r4wabr/karabas_pro/docs/photos/karabas-pro-revB-top.png

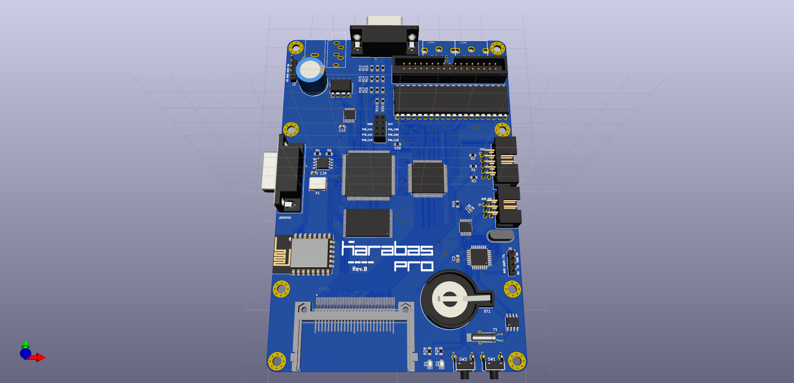
docs/photos/karabas-pro-revB-top.png
