r4wabr/karabas_pro/docs/photos/karabas-pro-revC-back.png

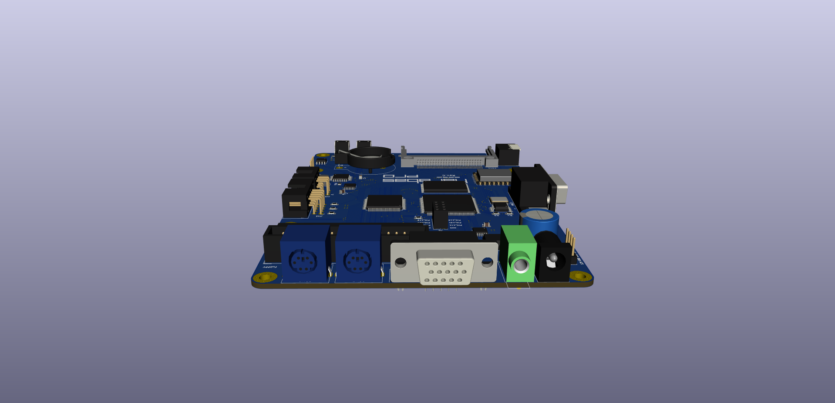
docs/photos/karabas-pro-revC-back.png
