r4wabr/karabas_pro/docs/photos/karabas-pro-revC-bot.png

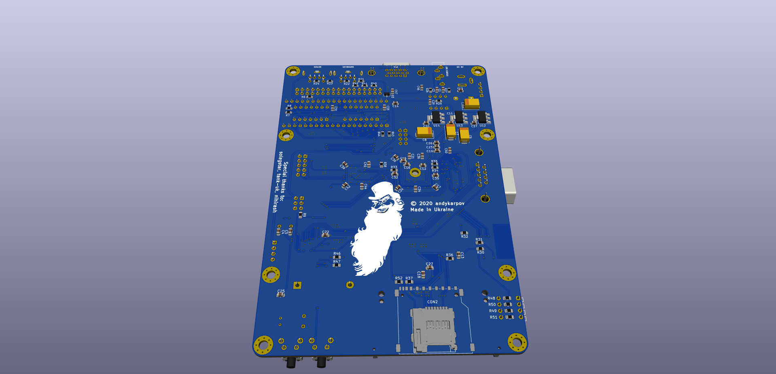
docs/photos/karabas-pro-revC-bot.png
