r4wabr/karabas_pro/docs/photos/karabas-pro-revC-top.png

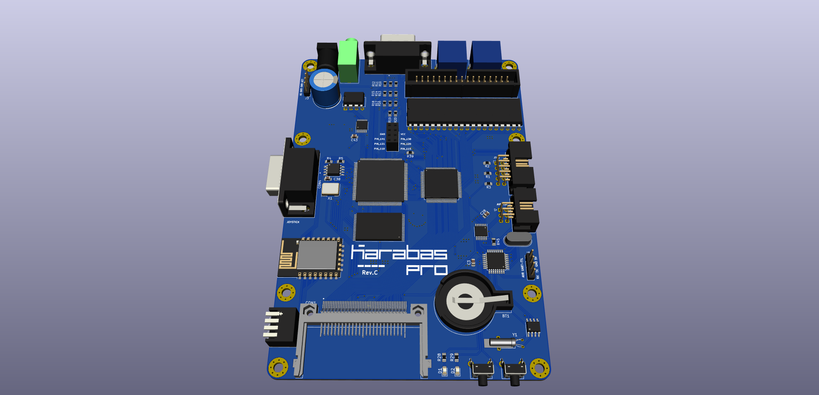
docs/photos/karabas-pro-revC-top.png
