r4wabr/karabas_pro/docs/photos/karabas-pro-revD-top.png

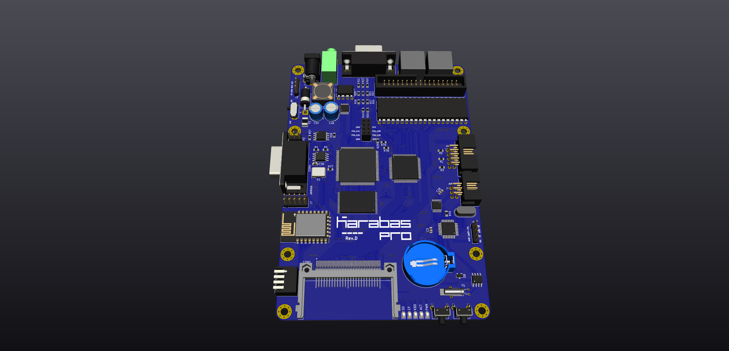
docs/photos/karabas-pro-revD-top.png
