r4wabr/karabas_pro/docs/photos/karabas-pro-revE-bot.png

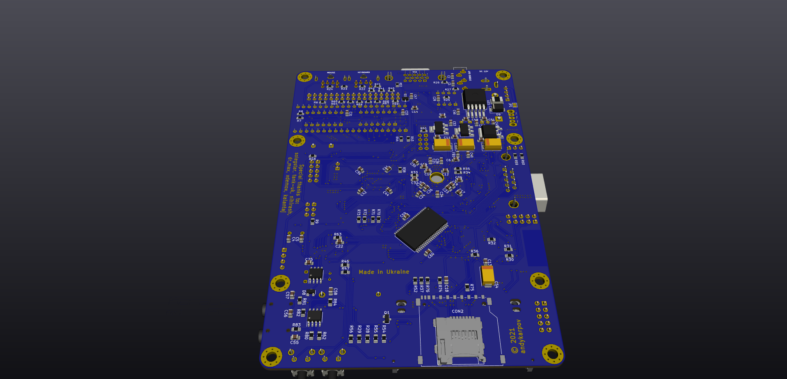
docs/photos/karabas-pro-revE-bot.png
