r4wabr/karabas_pro/docs/photos/karabas-pro-revE-top.png

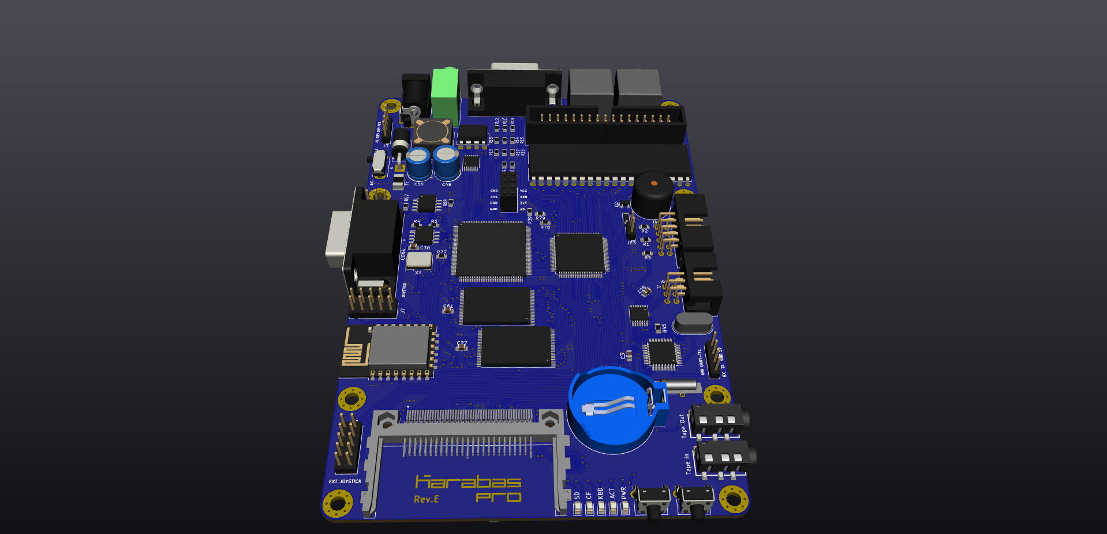
docs/photos/karabas-pro-revE-top.png
