r4wabr/karabas_pro/docs/photos/karabas-pro-revER-bottom.png

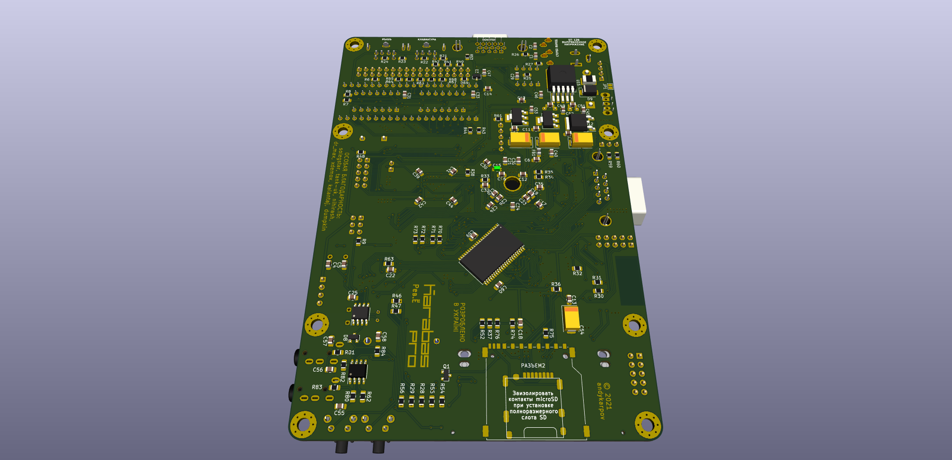
docs/photos/karabas-pro-revER-bottom.png
