r4wabr/karabas_pro/docs/karabas-pro-revD.pdf

# File: karabas-pro-revD.sch Sheet: / 100n C¹¹C7

# R10 2k R11 1k R12 510 R13 2k R14 1k R15 510 R16 2k R17 1k GND

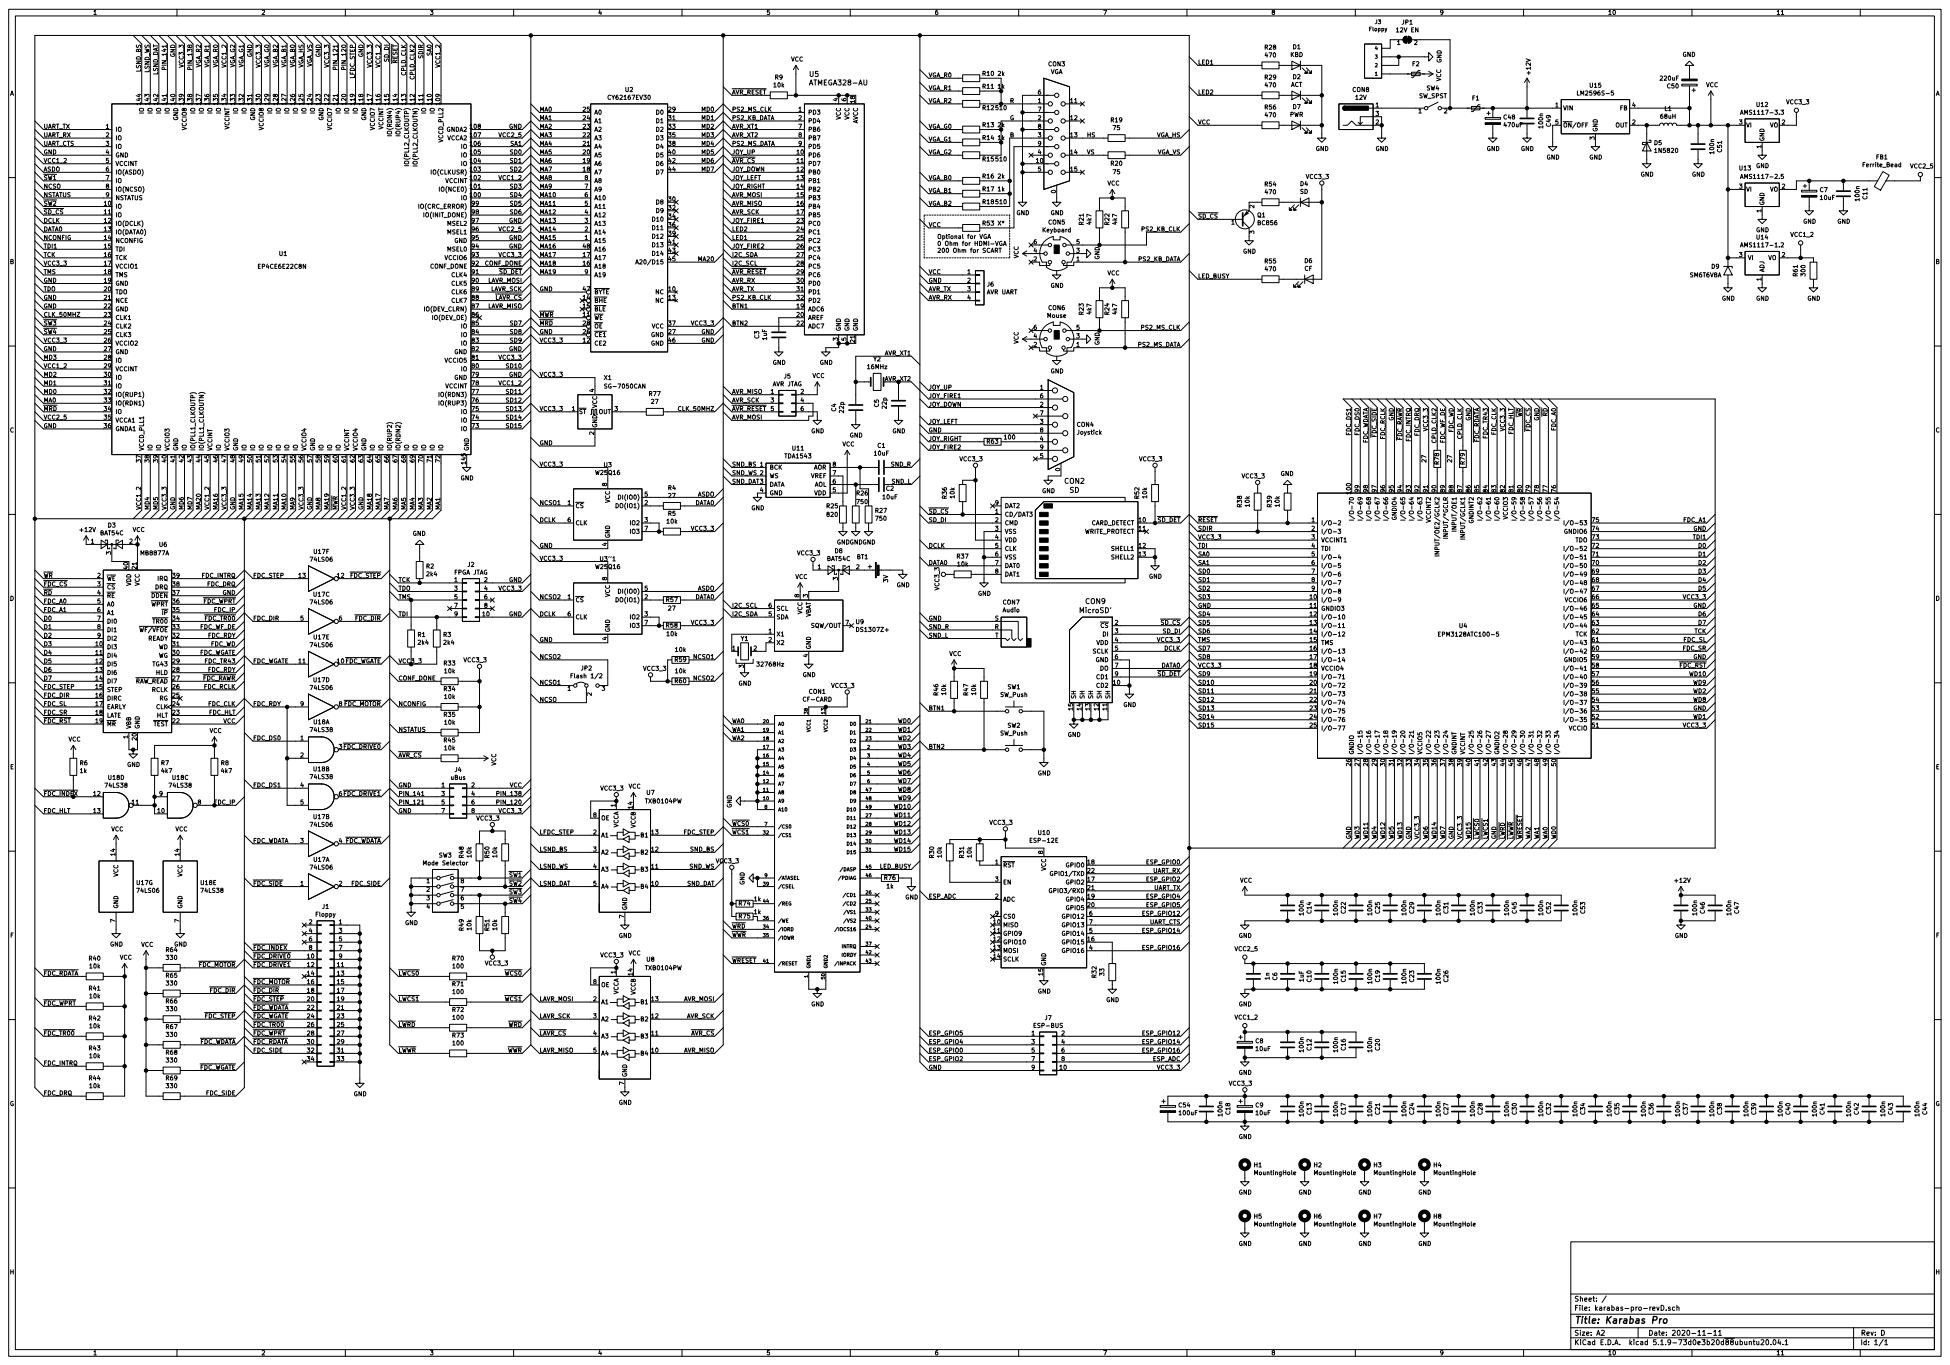
[picture p52: page 1]

6 PB6 7 PB7 8 PD5 9 PD6 10 AREF 20 PD0 30 PD7 11 GND 21 PD1 31 PB0 12 ADC7 22 PD2 32 PB1 13 PC0 23 PB2 14 PC1 24 PB3 15 PC2 25 PB4 16 PC3 26 PB5 17 PC4 27 AVCC 18 PC5 28 ADC6 19 PC6 29 U5ATMEGA328-AU

IO 2 TDO 20 NCE 21 GND 22 CLK1 23 CLK2 24 CLK3 25 VCCIO2 26 GND 27

Optional for VGA
0 Ohm for HDMI-VGA
200 Ohm for SCART

TDI 15 TCK 16 VCCIO1 17 TMS 18 GND 19
VCC1_2 TDO
VCC3_3 CLK_50MHZ GND

IP 35 WPRT 36 DDEN 37 DRQ 38

4 SDA 5 SCL 6 SQW/OUT 7 VCC

Id: 1/1 Title: Karabas Pro

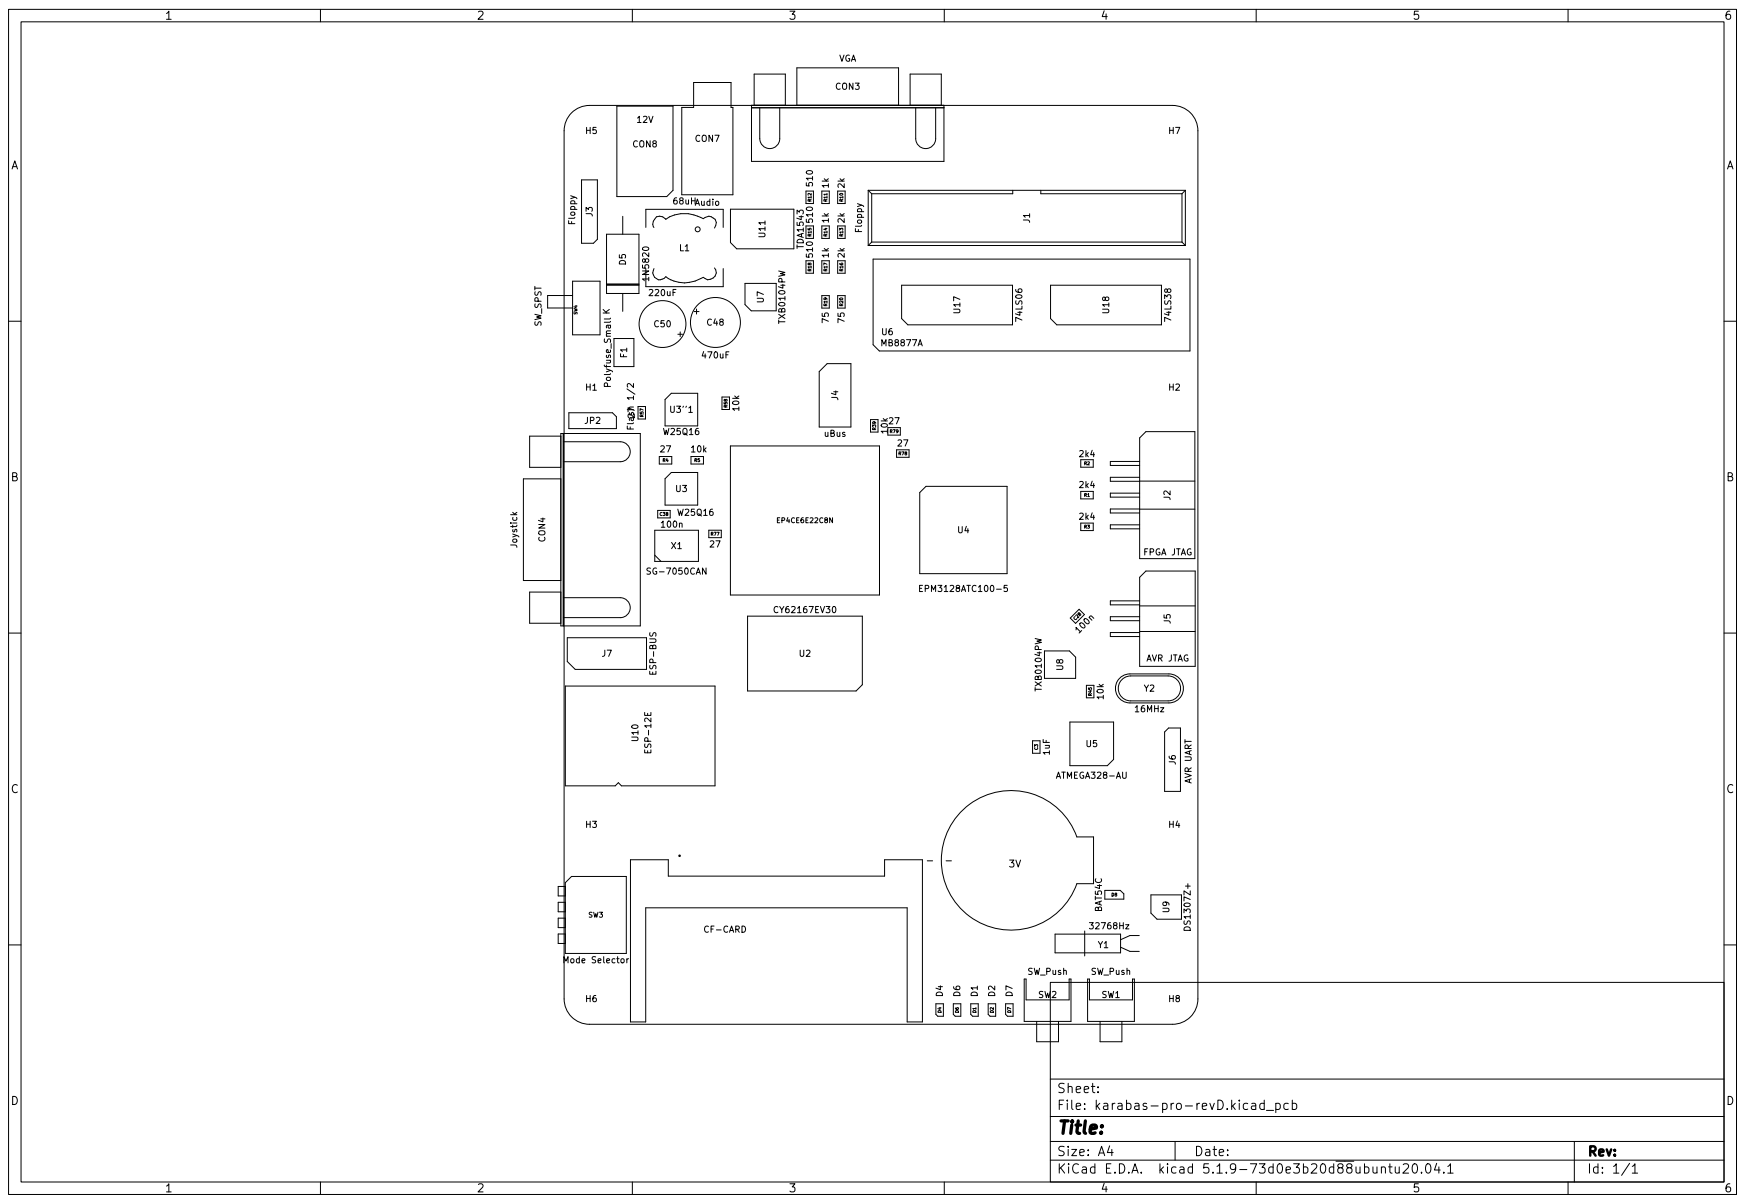
[picture p53: page 2]

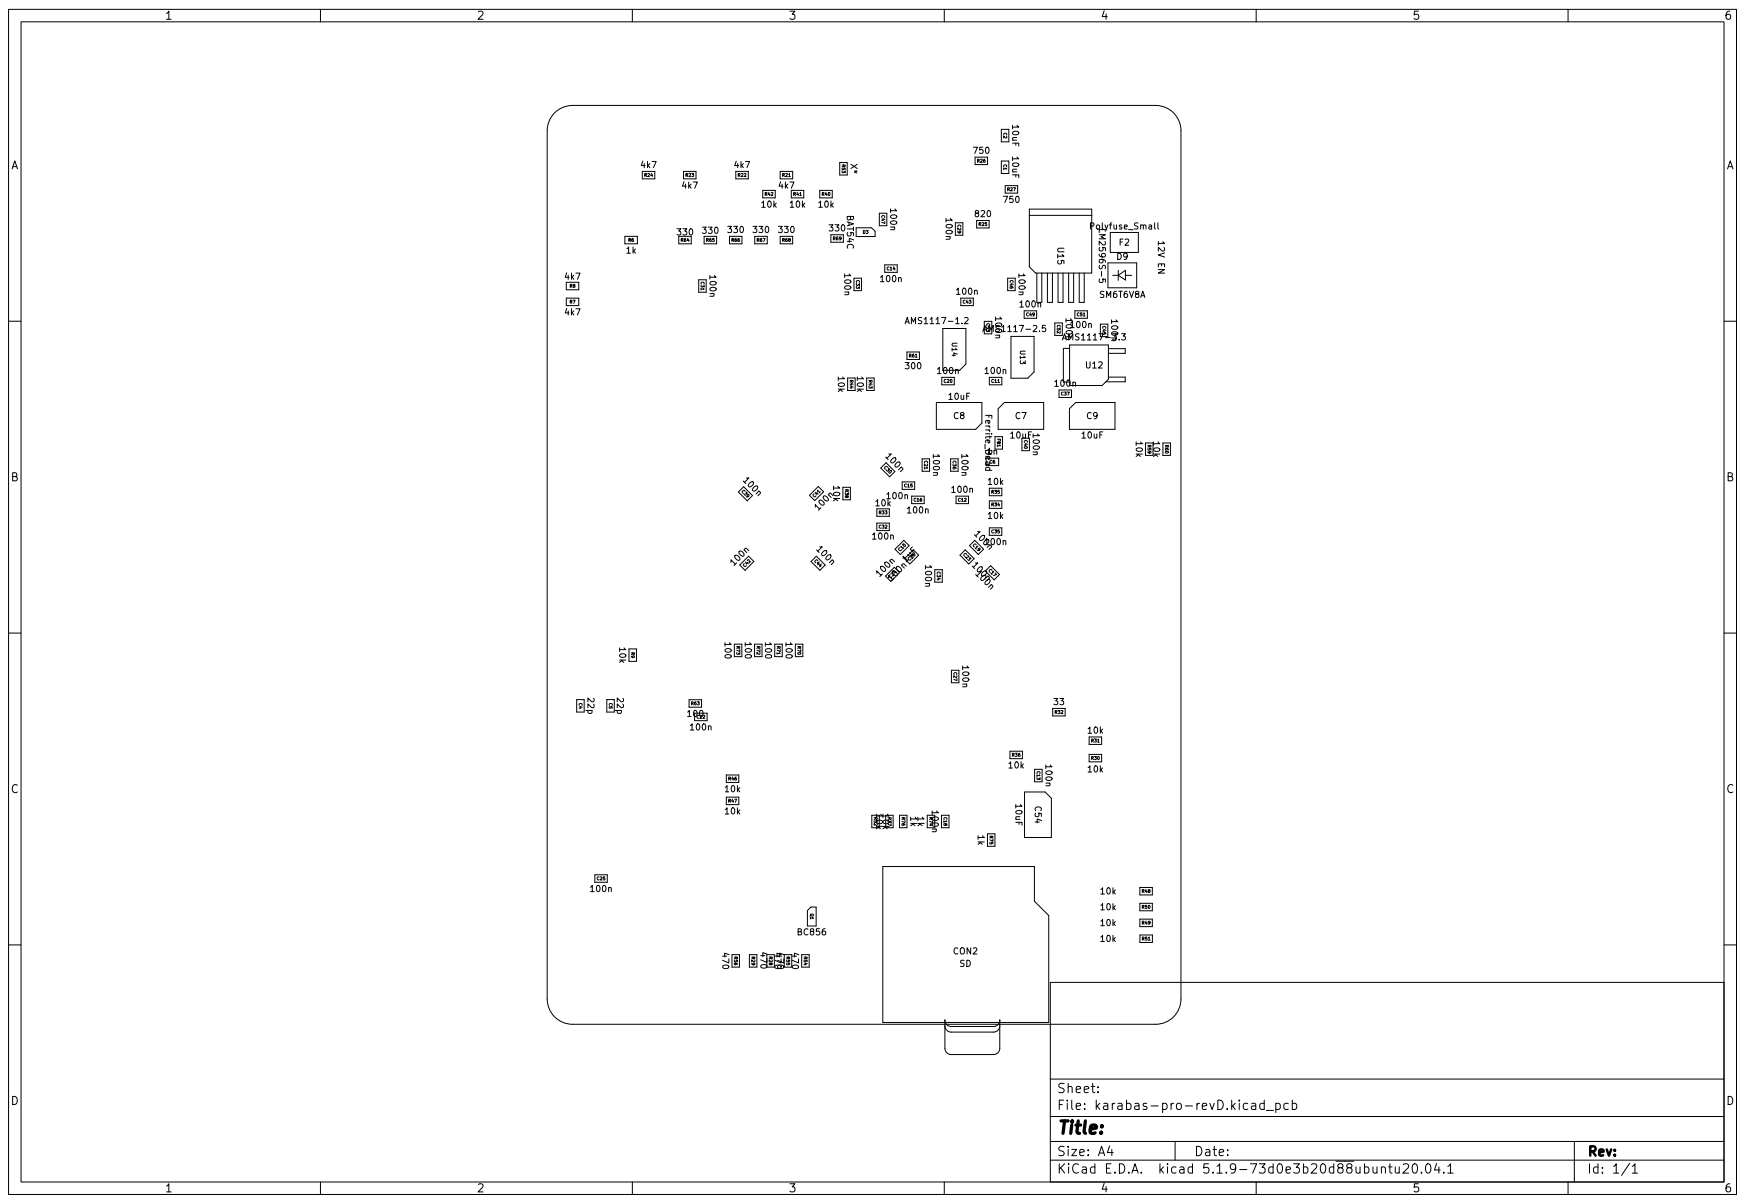
[picture p54: page 3]
